JosephBrooksbank/desk-hub/PCB/Review Files/fCu_pcb.png

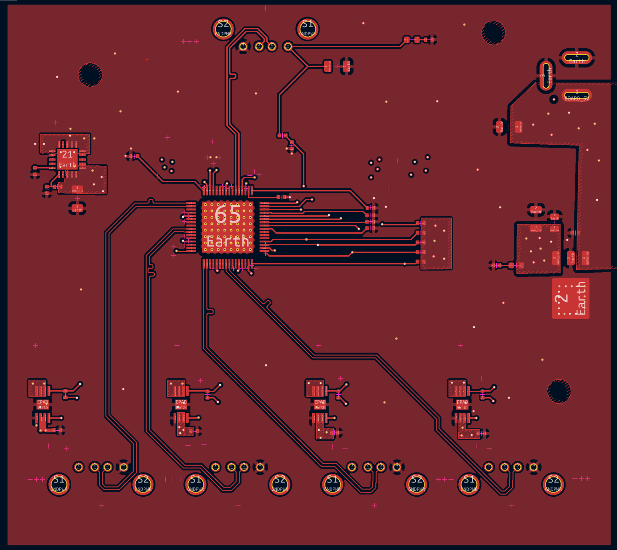
PCB/Review Files/fCu_pcb.png
